feynmantf/unsplit-keyboard/early revisions/manual wiring images/left half of the pcb shorted.jpg

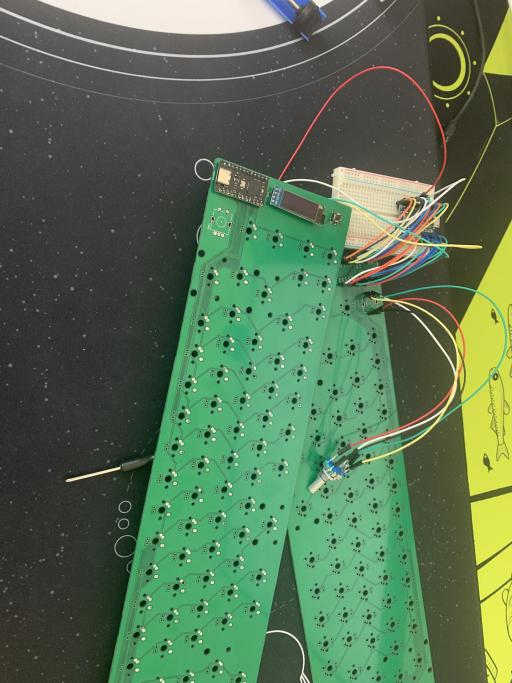
early revisions/manual wiring images/left half of the pcb shorted.jpg
