feynmantf/unsplit-keyboard/early revisions/final but with microcontrollers/plate and case files/gen settings.png

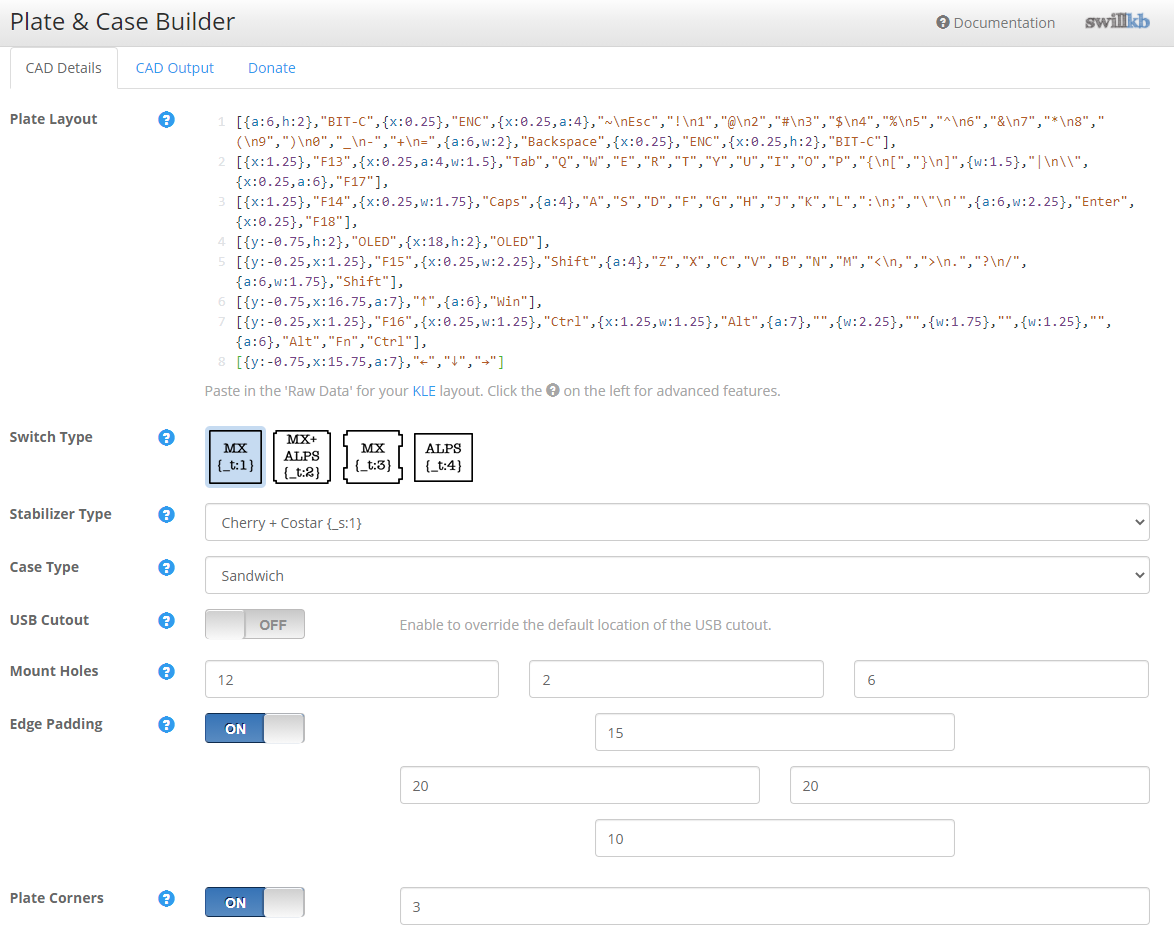
early revisions/final but with microcontrollers/plate and case files/gen settings.png
