feynmantf/unsplit-keyboard/early revisions/microcontroller versions/refrences/oled display dimensions.png

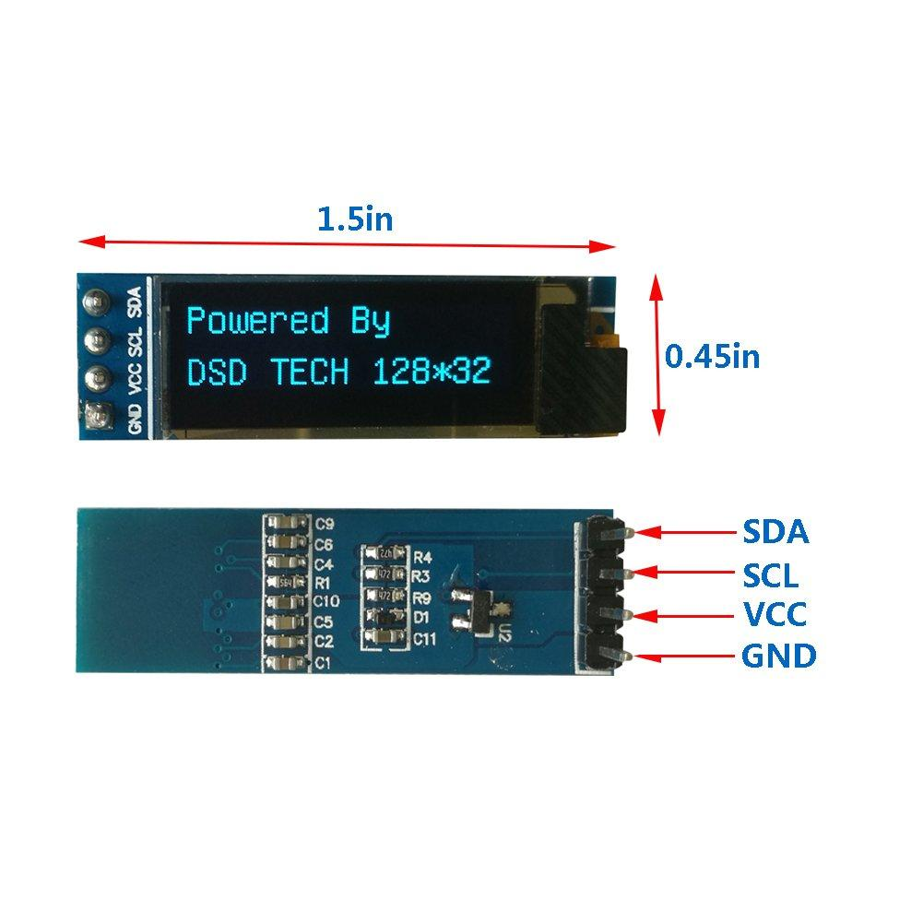
early revisions/microcontroller versions/refrences/oled display dimensions.png
