feynmantf/unsplit-keyboard/early revisions/microcontroller versions/refrences/SparkFun_Pro_Micro_Board_Dimensions.png

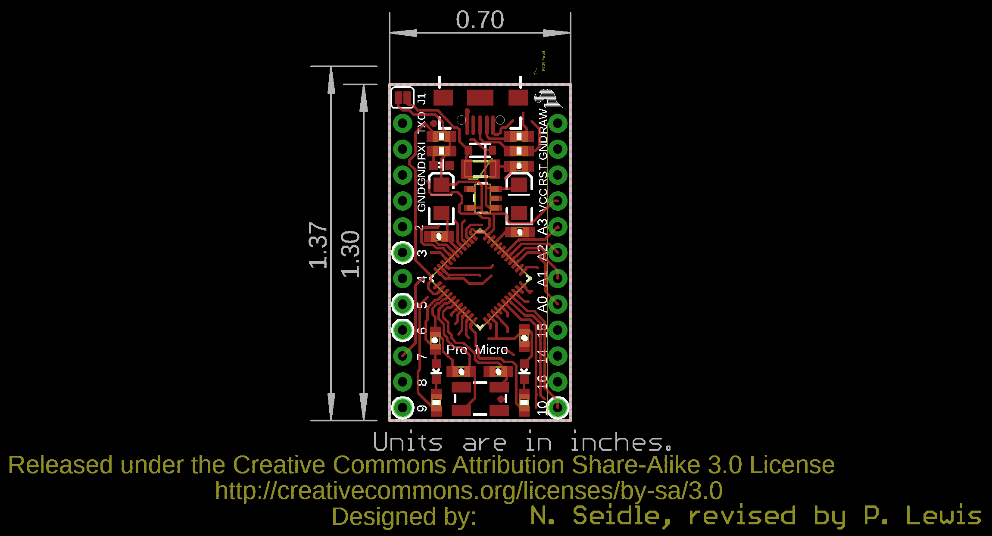
early revisions/microcontroller versions/refrences/SparkFun_Pro_Micro_Board_Dimensions.png
